Noteolvides/CubeTouch/website/docs/firstSteps/assets/Back/Back-back.png

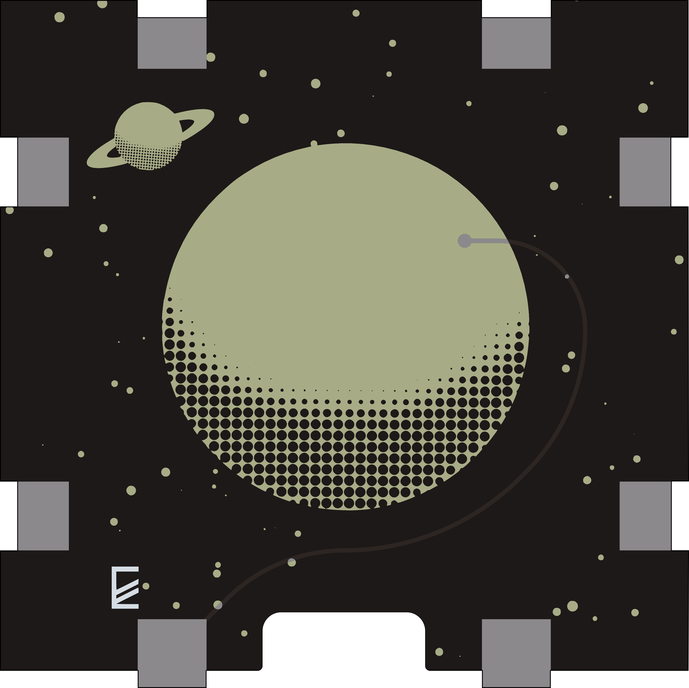
website/docs/firstSteps/assets/Back/Back-back.png
