Noteolvides/CubeTouch/website/docs/firstSteps/assets/Back/Back.png

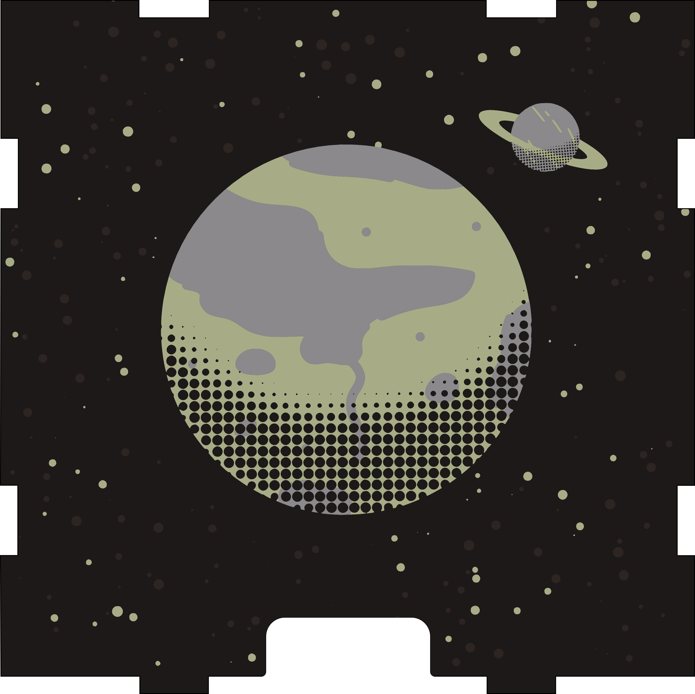
website/docs/firstSteps/assets/Back/Back.png
