Noteolvides/CubeTouch/website/docs/firstSteps/assets/EasyRGB.png

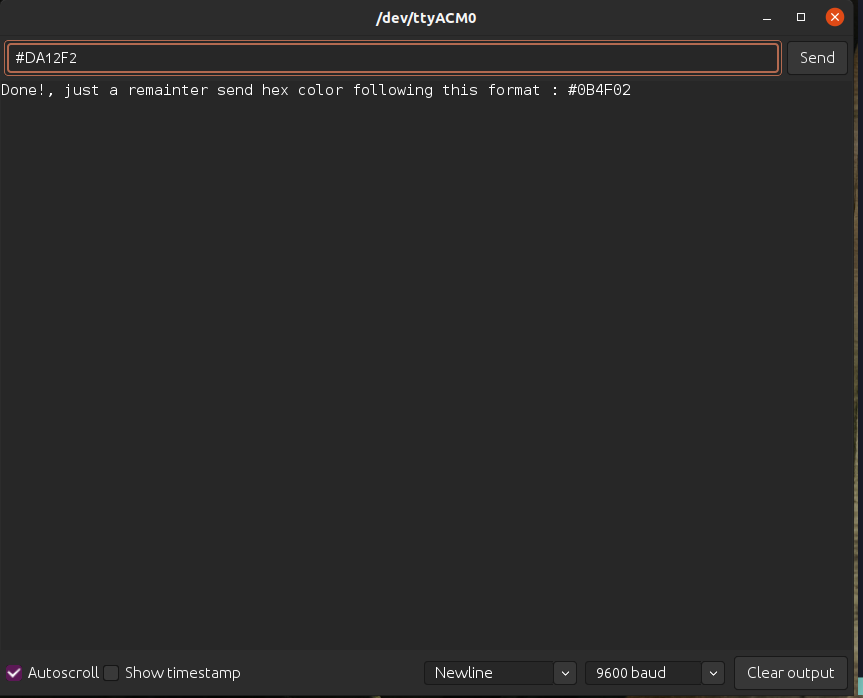
website/docs/firstSteps/assets/EasyRGB.png
