Noteolvides/CubeTouch/website/docs/firstSteps/assets/Front/Front-back.png

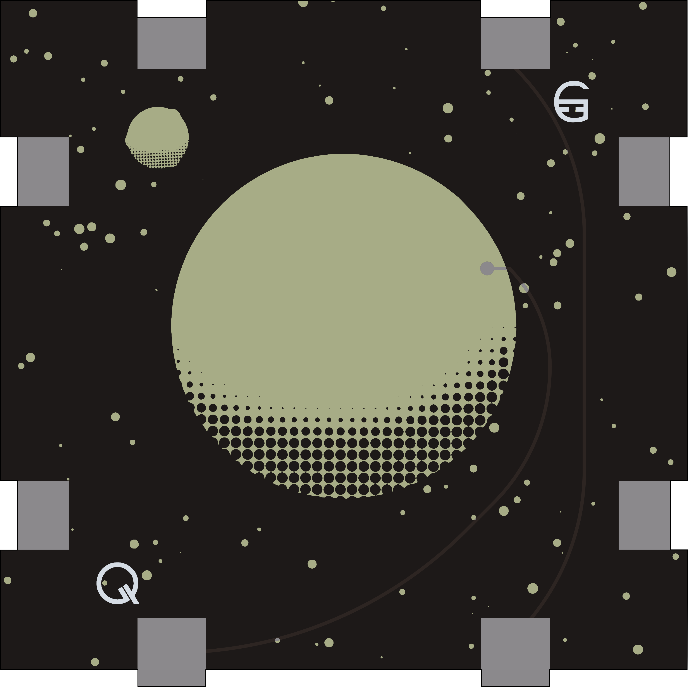
website/docs/firstSteps/assets/Front/Front-back.png
