Noteolvides/CubeTouch/website/docs/firstSteps/assets/Left/Left-back.png

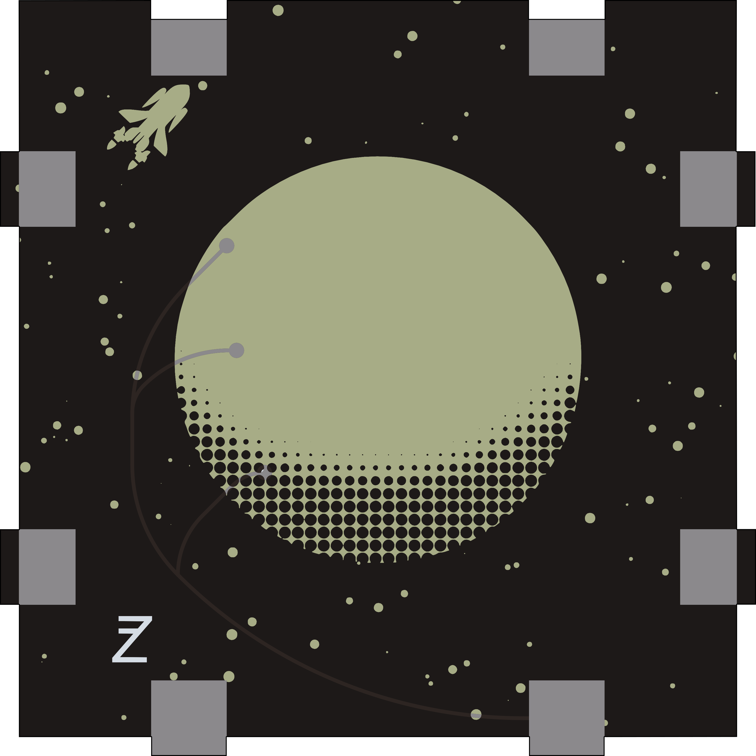
website/docs/firstSteps/assets/Left/Left-back.png
