Noteolvides/CubeTouch/website/docs/firstSteps/assets/Right/Right-back.png

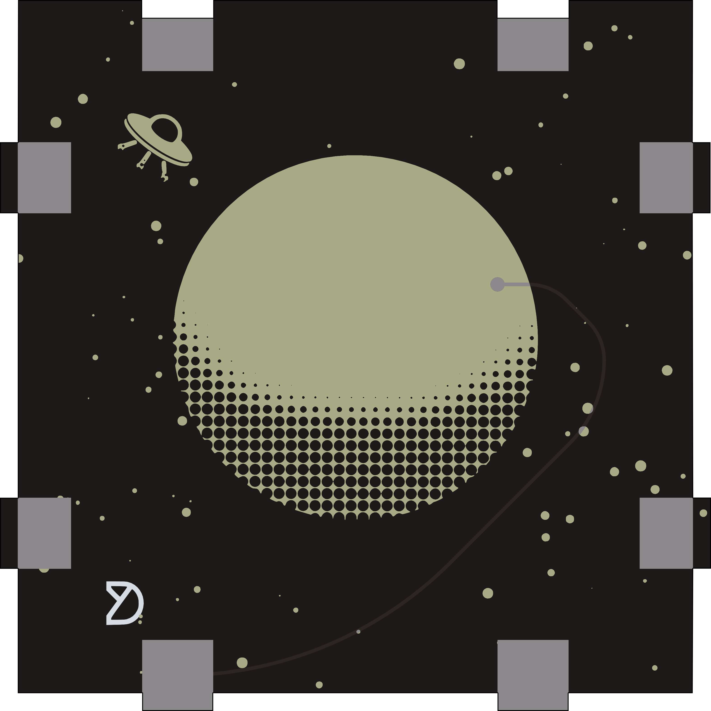
website/docs/firstSteps/assets/Right/Right-back.png
