Noteolvides/CubeTouch/website/docs/firstSteps/assets/Right/Right.png

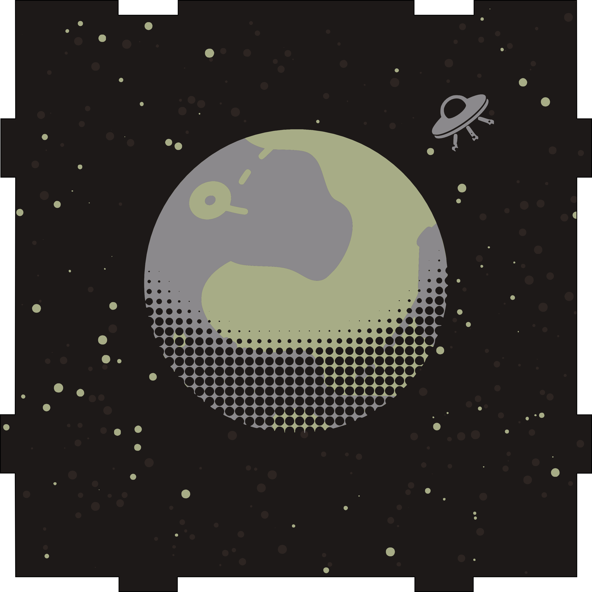
website/docs/firstSteps/assets/Right/Right.png
