Noteolvides/CubeTouch/website/docs/firstSteps/assets/Top/Top-back.png

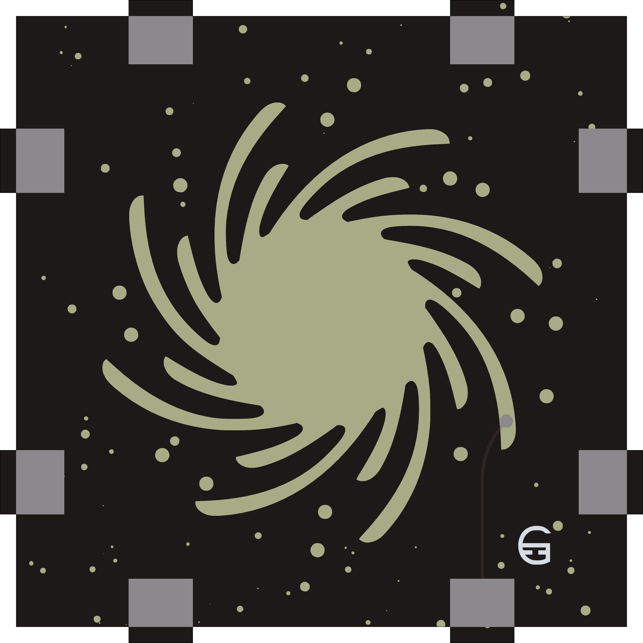
website/docs/firstSteps/assets/Top/Top-back.png
